leonidasdeim/th-app-project/th-api/src/main/java/com/deimantas/thapi/security/WebSecurityConfig.java

package com.deimantas.thapi.security;

import com.deimantas.thapi.security.jwt.AuthEntryPointJwt;
import com.deimantas.thapi.security.jwt.AuthTokenFilter;
import org.springframework.beans.factory.annotation.Qualifier;
import org.springframework.context.annotation.Bean;
import org.springframework.context.annotation.Configuration;
import org.springframework.http.HttpMethod;
import org.springframework.security.authentication.AuthenticationManager;
import org.springframework.security.config.annotation.authentication.builders.AuthenticationManagerBuilder;
import org.springframework.security.config.annotation.method.configuration.EnableGlobalMethodSecurity;
import org.springframework.security.config.annotation.web.builders.HttpSecurity;
import org.springframework.security.config.annotation.web.configuration.EnableWebSecurity;
import org.springframework.security.config.annotation.web.configuration.WebSecurityConfigurerAdapter;
import org.springframework.security.config.http.SessionCreationPolicy;
import org.springframework.security.core.userdetails.UserDetailsService;
import org.springframework.security.crypto.bcrypt.BCryptPasswordEncoder;
import org.springframework.security.crypto.password.PasswordEncoder;
import org.springframework.security.web.authentication.UsernamePasswordAuthenticationFilter;
import org.springframework.security.web.firewall.HttpFirewall;
import org.springframework.security.web.firewall.StrictHttpFirewall;

@Configuration
@EnableWebSecurity
@EnableGlobalMethodSecurity(
		// securedEnabled = true,
		// jsr250Enabled = true,
		prePostEnabled = true)
public class WebSecurityConfig extends WebSecurityConfigurerAdapter {
	private final UserDetailsService userDetailsService;
	private final AuthTokenFilter authTokenFilter;
	private final AuthEntryPointJwt authEntryPointJwt;

	public WebSecurityConfig(
			@Qualifier("userDetailsServiceImpl") UserDetailsService userDetailsService,
			AuthTokenFilter authTokenFilter,
			AuthEntryPointJwt authEntryPointJwt) {
		this.userDetailsService = userDetailsService;
		this.authTokenFilter = authTokenFilter;
		this.authEntryPointJwt = authEntryPointJwt;
	}

	@Bean
	@Override
	public AuthenticationManager authenticationManagerBean() throws Exception {
		return super.authenticationManagerBean();
	}

	@Bean
	public PasswordEncoder passwordEncoder() {
		return new BCryptPasswordEncoder();
	}

	@Override
	public void configure(AuthenticationManagerBuilder authenticationManagerBuilder) throws Exception {
		authenticationManagerBuilder.userDetailsService(userDetailsService).passwordEncoder(passwordEncoder());
	}

	@Bean
	public HttpFirewall looseHttpFirewall() {
		StrictHttpFirewall firewall = new StrictHttpFirewall();
		firewall.setAllowSemicolon(true);
		firewall.setAllowUrlEncodedPercent(true);
		firewall.setAllowUrlEncodedSlash(true);
		firewall.setAllowUrlEncodedPeriod(true);
		firewall.setAllowUrlEncodedDoubleSlash(true);
		firewall.setAllowBackSlash(true);
		return firewall;
	}

	@Override
	protected void configure(HttpSecurity http) throws Exception {
		http.cors().and().csrf().disable()
			.exceptionHandling().authenticationEntryPoint(authEntryPointJwt).and()
			.sessionManagement().sessionCreationPolicy(SessionCreationPolicy.STATELESS).and()
			.authorizeRequests().antMatchers("/auth/**").permitAll()
				.antMatchers(HttpMethod.POST, "/sensor/**").permitAll()
				.antMatchers(HttpMethod.POST, "/data/**").permitAll()
				.antMatchers("/manufacture/**").hasRole("ADMIN")
				.anyRequest().authenticated();

		http.addFilterBefore(authTokenFilter, UsernamePasswordAuthenticationFilter.class);
	}
}
